vekexasia/comfoair-esp32/components/comfoair/commands.h

#pragma once

#define CMD_ventilation_level_0             { 0x84, 0x15, 0x01, 0x01, 0x00, 0x00, 0x00, 0x00, 0x01, 0x00, 0x00, 0x00, 0x00 }
#define CMD_ventilation_level_1             { 0x84, 0x15, 0x01, 0x01, 0x00, 0x00, 0x00, 0x00, 0x01, 0x00, 0x00, 0x00, 0x01 }
#define CMD_ventilation_level_2             { 0x84, 0x15, 0x01, 0x01, 0x00, 0x00, 0x00, 0x00, 0x01, 0x00, 0x00, 0x00, 0x02 }
#define CMD_ventilation_level_3             { 0x84, 0x15, 0x01, 0x01, 0x00, 0x00, 0x00, 0x00, 0x01, 0x00, 0x00, 0x00, 0x03 }
#define CMD_boost_10_min                    { 0x84, 0x15, 0x01, 0x06, 0x00, 0x00, 0x00, 0x00, 0x58, 0x02, 0x00, 0x00, 0x03, 0x00, 0x00, 0x00 }
#define CMD_boost_20_min                    { 0x84, 0x15, 0x01, 0x06, 0x00, 0x00, 0x00, 0x00, 0xB0, 0x04, 0x00, 0x00, 0x03, 0x00, 0x00, 0x00 }
#define CMD_boost_30_min                    { 0x84, 0x15, 0x01, 0x06, 0x00, 0x00, 0x00, 0x00, 0x08, 0x07, 0x00, 0x00, 0x03, 0x00, 0x00, 0x00 }
#define CMD_boost_60_min                    { 0x84, 0x15, 0x01, 0x06, 0x00, 0x00, 0x00, 0x00, 0x10, 0x0E, 0x00, 0x00, 0x03, 0x00, 0x00, 0x00 }
#define CMD_boost_end                       { 0x85, 0x15, 0x01, 0x06 }
#define CMD_auto                            { 0x85, 0x15, 0x08, 0x01 }
#define CMD_manual                          { 0x84, 0x15, 0x08, 0x01, 0x00, 0x00, 0x00, 0x00, 0x01, 0x00, 0x00, 0x00, 0x01 }
#define CMD_bypass_activate_1h              { 0x84, 0x15, 0x02, 0x01, 0x00, 0x00, 0x00, 0x00, 0x10, 0x0e, 0x00, 0x00, 0x01 }
#define CMD_bypass_deactivate_1h            { 0x84, 0x15, 0x02, 0x01, 0x00, 0x00, 0x00, 0x00, 0x10, 0x0e, 0x00, 0x00, 0x02 }
#define CMD_bypass_auto                     { 0x85, 0x15, 0x02, 0x01 }
#define CMD_ventilation_supply_only         { 0x84, 0x15, 0x06, 0x01, 0x00, 0x00, 0x00, 0x00, 0x10, 0x0e, 0x00, 0x00, 0x01 }
#define CMD_ventilation_supply_only_reset   { 0x85, 0x15, 0x06, 0x01 }
#define CMD_ventilation_extract_only        { 0x84, 0x15, 0x07, 0x01, 0x00, 0x00, 0x00, 0x00, 0x10, 0x0e, 0x00, 0x00, 0x00 }
#define CMD_ventilation_extract_only_reset  { 0x85, 0x15, 0x07, 0x01 }
#define CMD_temp_profile_normal             { 0x84, 0x15, 0x03, 0x01, 0x00, 0x00, 0x00, 0x00, 0xff, 0xff, 0xff, 0xff, 0x00 }
#define CMD_temp_profile_cool               { 0x84, 0x15, 0x03, 0x01, 0x00, 0x00, 0x00, 0x00, 0xff, 0xff, 0xff, 0xff, 0x01 }
#define CMD_temp_profile_warm               { 0x84, 0x15, 0x03, 0x01, 0x00, 0x00, 0x00, 0x00, 0xff, 0xff, 0xff, 0xff, 0x02 }
